smallwat3r/rpi-gardener/rpi/logging.py

"""Logging configuration for the RPi Gardener application."""

import logging
import sys

LOG_FORMAT = "%(asctime)s %(name)s %(levelname)s - %(message)s"


def configure(level: int = logging.INFO) -> None:
    """Configure logging for the application.

    Safe to call multiple times, the handler is only attached once.
    """
    root = logging.getLogger("rpi")
    root.setLevel(level)
    if root.handlers:
        return

    handler = logging.StreamHandler(sys.stderr)
    handler.setFormatter(logging.Formatter(LOG_FORMAT))
    root.addHandler(handler)

    # Configure uvicorn root logger to use the same format
    # (child loggers like uvicorn.error propagate to this)
    uv_log = logging.getLogger("uvicorn")
    uv_log.handlers.clear()
    uv_log.addHandler(handler)


def get_logger(name: str) -> logging.Logger:
    """Get a logger under the 'rpi' namespace.

    Args:
        name: Logger name (will be prefixed with 'rpi.')

    Returns:
        Configured logger instance.
    """
    return logging.getLogger(f"rpi.{name}")
