smallwat3r/rpi-gardener/rpi/dht/service.py

"""Event handling and auditing service for the DHT22 sensor.

The service is responsible for:
- Auditing readings against predefined thresholds
- Queuing notification events when thresholds are crossed
- Processing events via a background worker thread
"""
from queue import Queue
from threading import Thread

from rpi.dht.models import Measure, Reading, State
from rpi.lib.alerts import (AlertState, Namespace, ThresholdViolation,
                            get_alert_tracker)
from rpi.lib.config import THRESHOLD_RULES
from rpi.lib.notifications import get_notifier
from rpi.logging import get_logger

logger = get_logger("dht.service")

_queue: Queue[ThresholdViolation] = Queue()


def _enqueue_event(violation: ThresholdViolation) -> None:
    """Enqueue a violation for processing by the background worker."""
    _queue.put(violation)


def _event_worker() -> None:
    """Process events from the queue (blocks until event available)."""
    notifier = get_notifier()
    while True:
        violation = _queue.get()
        logger.info("Processing alert for %s", violation.sensor_name)
        notifier.send(violation)
        _queue.task_done()


def start_worker() -> None:
    """Start the background worker thread for processing events."""
    tracker = get_alert_tracker()
    tracker.register_callback(Namespace.DHT, _enqueue_event)
    Thread(target=_event_worker, daemon=True).start()


def audit_reading(reading: Reading) -> None:
    """Audit reading values against thresholds and enqueue notification events."""
    tracker = get_alert_tracker()

    for name, rules in THRESHOLD_RULES.items():
        measure: Measure = getattr(reading, name)

        # Check each rule for this measure
        for comparator, threshold in rules:
            is_violated = comparator(measure.value, threshold)
            if is_violated:
                alert_state = tracker.check(
                    namespace=Namespace.DHT,
                    sensor_name=name,
                    value=measure.value,
                    unit=str(measure.unit),
                    threshold=threshold,
                    is_violated=True,
                    recording_time=reading.recording_time,
                )
                measure.state = State.IN_ALERT if alert_state == AlertState.IN_ALERT else State.OK
                break
        else:
            # No threshold violated
            tracker.check(
                namespace=Namespace.DHT,
                sensor_name=name,
                value=measure.value,
                unit=str(measure.unit),
                threshold=0,
                is_violated=False,
                recording_time=reading.recording_time,
            )
            measure.state = State.OK
